NeerajR18/version0.65/Assets/Keycaps/Tab_key.step

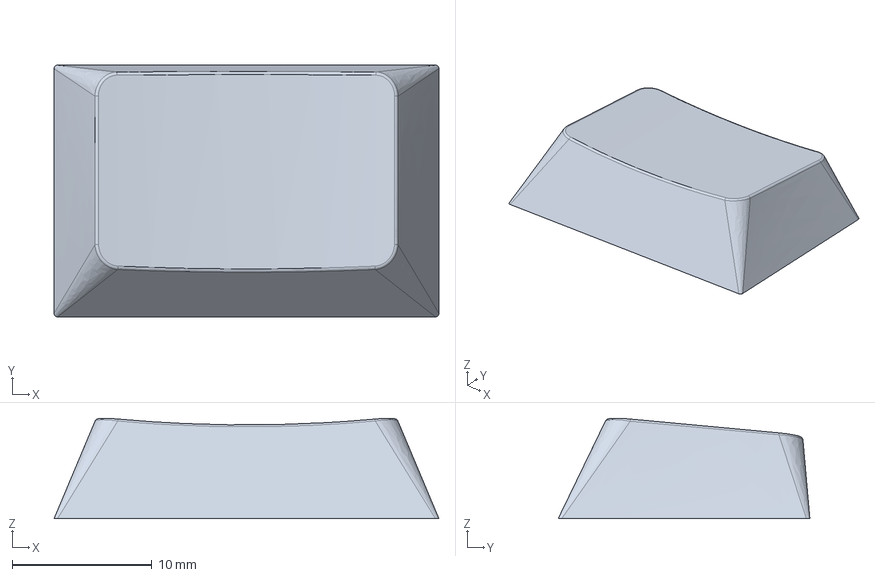
[picture p14: CAD file, 2026-06-14]
Assets/Keycaps/Tab_key.step
27.5 x 18.0 x 7.18 mm
