NeerajR18/version0.65/Assets/Keycaps/ESC_and_Function_keys.step

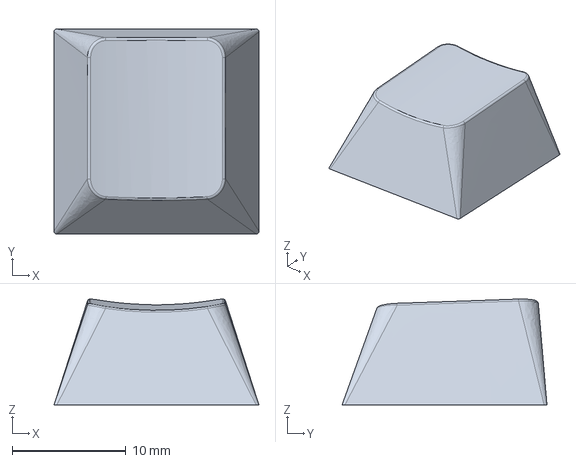
[picture p15: CAD file, 2026-06-14]
Assets/Keycaps/ESC_and_Function_keys.step
18.0 x 18.0 x 9.30 mm
