NeerajR18/version0.65/Assets/Keycaps/middle_row.step

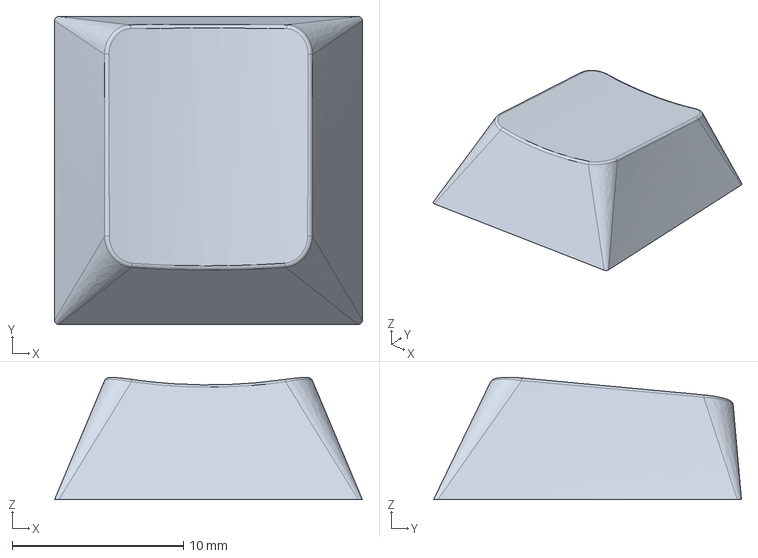
[picture p16: CAD file, 2026-06-14]
Assets/Keycaps/middle_row.step
18.0 x 18.0 x 7.15 mm
