NeerajR18/version0.65/Assets/Keycaps/Caps.step

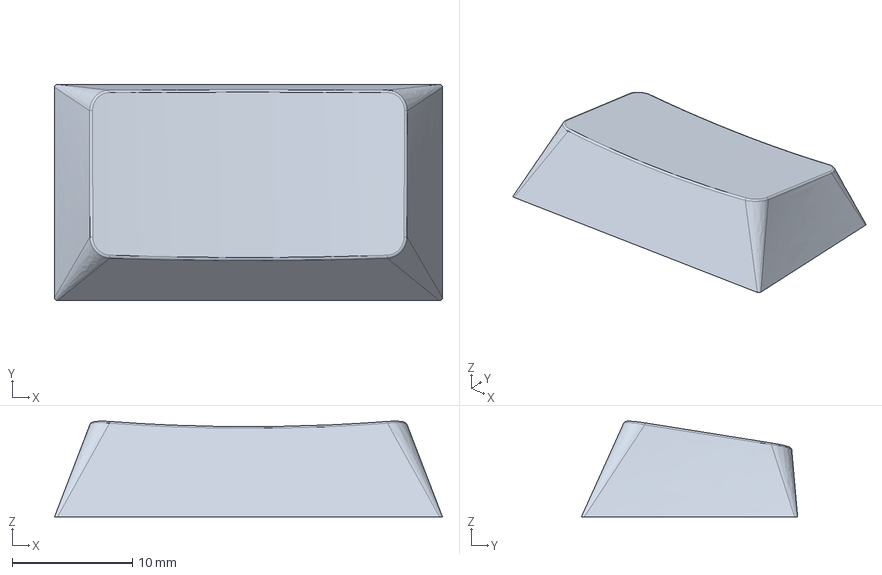
[picture p17: CAD file, 2026-06-14]
Assets/Keycaps/Caps.step
32.3 x 18.0 x 7.96 mm
