NeerajR18/version0.65/Assets/Keycaps/Back_sp.step

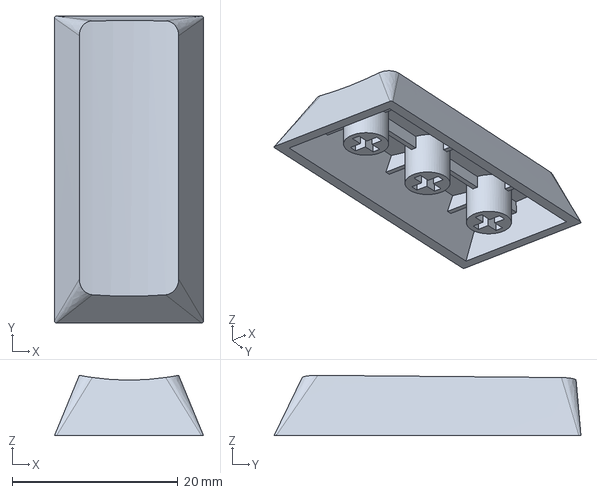
[picture p18: CAD file, 2026-06-14]
Assets/Keycaps/Back_sp.step
18.0 x 37.0 x 7.28 mm
