NeerajR18/version0.65/Assets/Keycaps/Space_bar.step

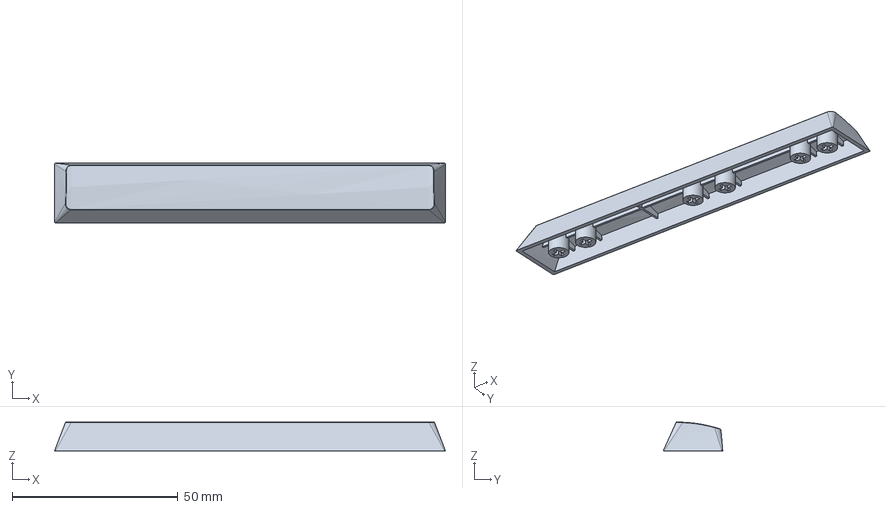
[picture p19: CAD file, 2026-06-14]
Assets/Keycaps/Space_bar.step
118.0 x 18.0 x 8.70 mm
